JoseAntonioMG/WeatherStation/pcb/Weather-Station-3DM.png

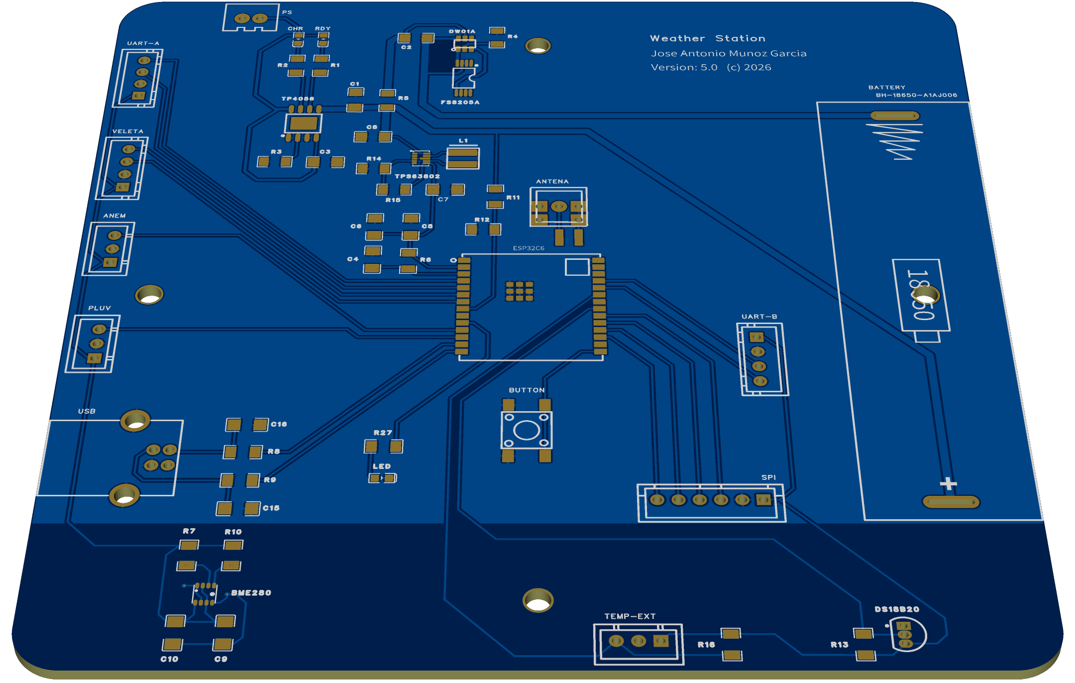
pcb/Weather-Station-3DM.png
