JoseAntonioMG/WeatherStation/pcb/Weather-Station-PCB.jpg

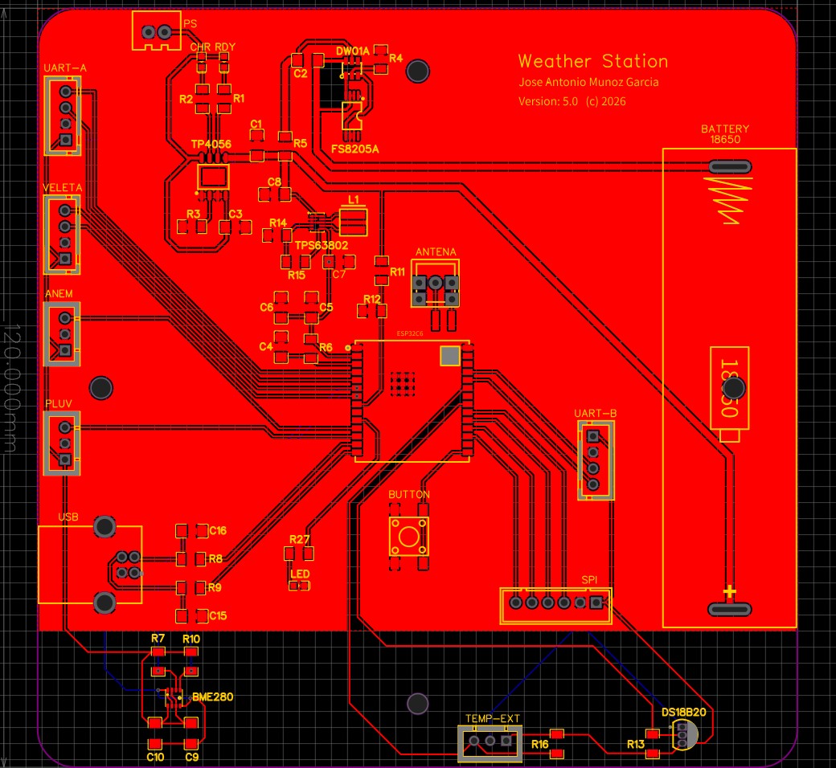
pcb/Weather-Station-PCB.jpg
